vladbalmos/pi-power-hub/hw/mosfet-drive-startup-and-simulation.asc

B1: bv; V=delay(V(3.3V), 500m)
C1: cap; 47n
C2: cap; 47n
C3: cap; 47n
C4: cap; 47n
C5: cap; 47n
C6: cap; 47n
M1: nmos; IRFZ44N
M2: nmos; IRFZ44N
M3: nmos; IRFZ44N
M4: nmos; IRFZ44N
M5: nmos; IRFZ44N
M6: nmos; IRFZ44N
Output1: res; 25
Output2: res; 25
Output3: res; 25
Output4: res; 25
Output5: res; 25
Output: res; 25
Pico_3.3V: voltage; 3.3
Q1: npn; 2N2222
Q2: pnp
Q3: npn; 2N2222
Q4: npn; 2N2222
Q5: npn; 2N2222
Q6: npn; 2N2222
Q7: npn; 2N2222
R1: res; 2k
R2: res; 2k
R3: res; 20k
R4: res; 15k
R5: res; 20k
R6: res; 2k
R7: res; 20k
R8: res; 2k
R9: res; 20k
R10: res; 2k
R11: res; 20k
R12: res; 2k
R13: res; 20k
R14: res; 15k
USB_5V: voltage; 5
V1: voltage; PULSE(0 3.3 0.5 20n 20n 1 2)
Named nets: 0, 5V, NPN_enable, 3.3V, PICO_output_pin
.tran 10 startup
0. Simulate PICO startup behaviour and toggling power MOSFET on/off
1. The PNP is used to turn on all NPN transistors while the PICO is initializing the micropython
code, thus keeping the MOSFETs off, preventing power flickering during startup
1. Emulate the PICO ready pin behavior
Pico Port 1
Pico Port 2
Pico Port 3
Pico Port 4
Pico Port 5
Pico Port 6
2. Emulate PICO pins turning on/off
